MostafaELFEEL/Amusement-Park-Themed-Marble-Track/Images of CAD+CAD file/2.PNG

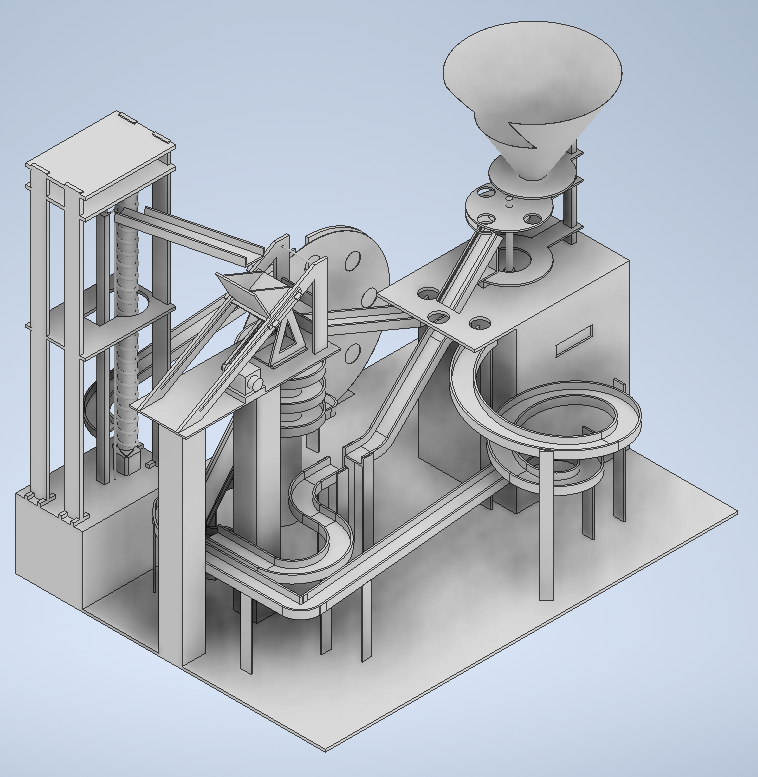
Images of CAD+CAD file/2.PNG
