MostafaELFEEL/Amusement-Park-Themed-Marble-Track/Images of CAD+CAD file/5.PNG

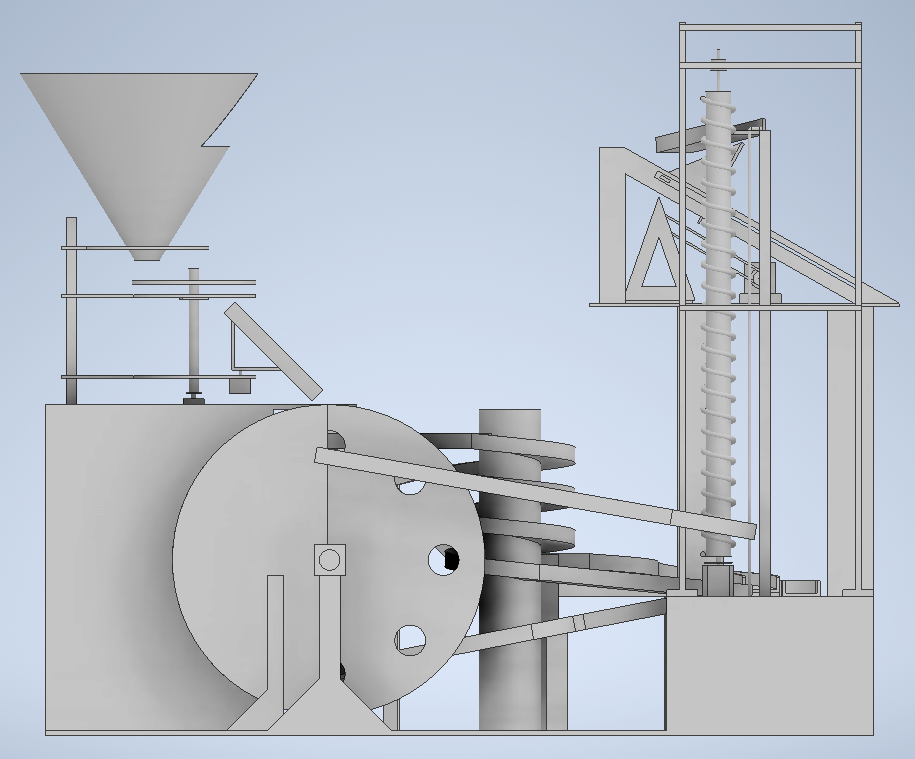
Images of CAD+CAD file/5.PNG
