MostafaELFEEL/Amusement-Park-Themed-Marble-Track/Images of CAD+CAD file/6.PNG

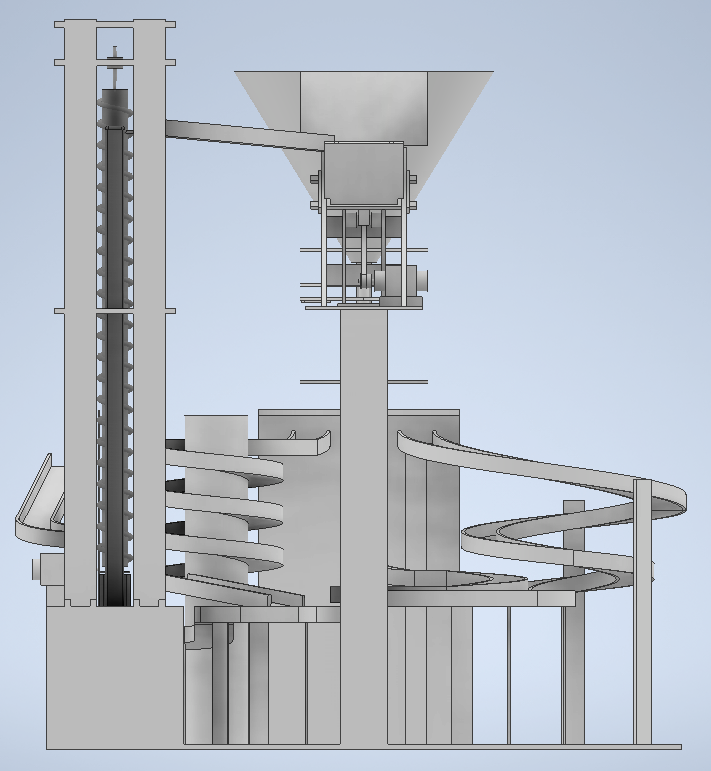
Images of CAD+CAD file/6.PNG
