MostafaELFEEL/Amusement-Park-Themed-Marble-Track/Images of CAD+CAD file/7.PNG

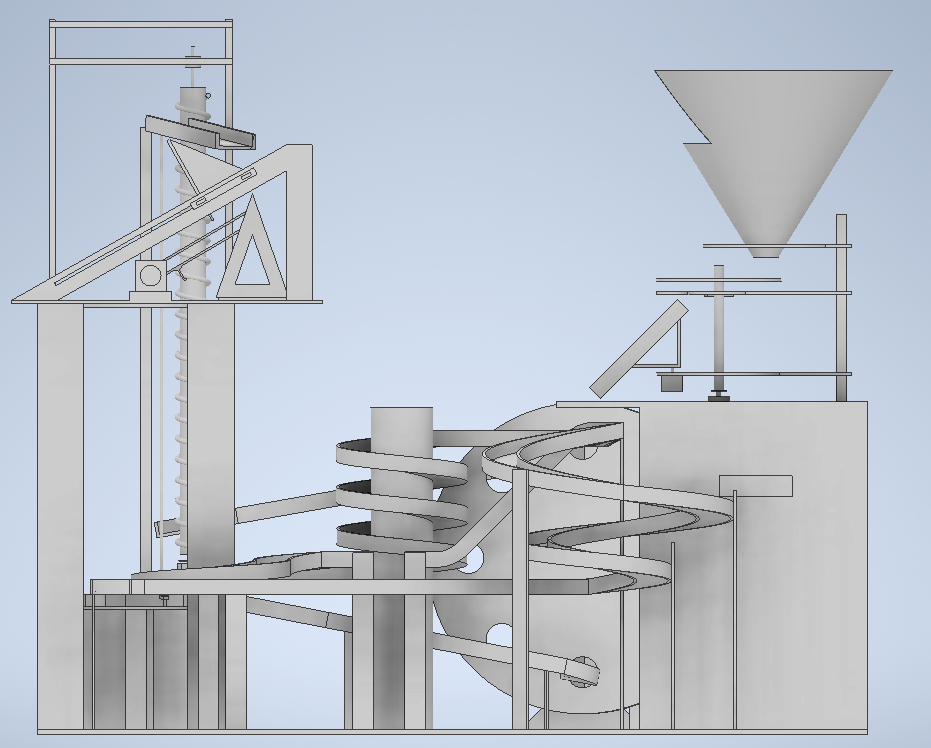
Images of CAD+CAD file/7.PNG
