MostafaELFEEL/Amusement-Park-Themed-Marble-Track/Images of CAD+CAD file/8.PNG

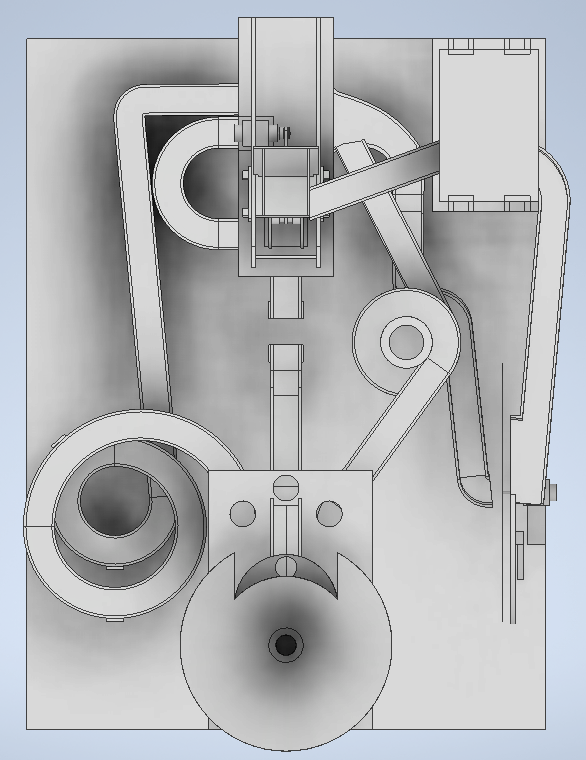
Images of CAD+CAD file/8.PNG
