MostafaELFEEL/Amusement-Park-Themed-Marble-Track/Images of CAD+CAD file/shooting 1.PNG

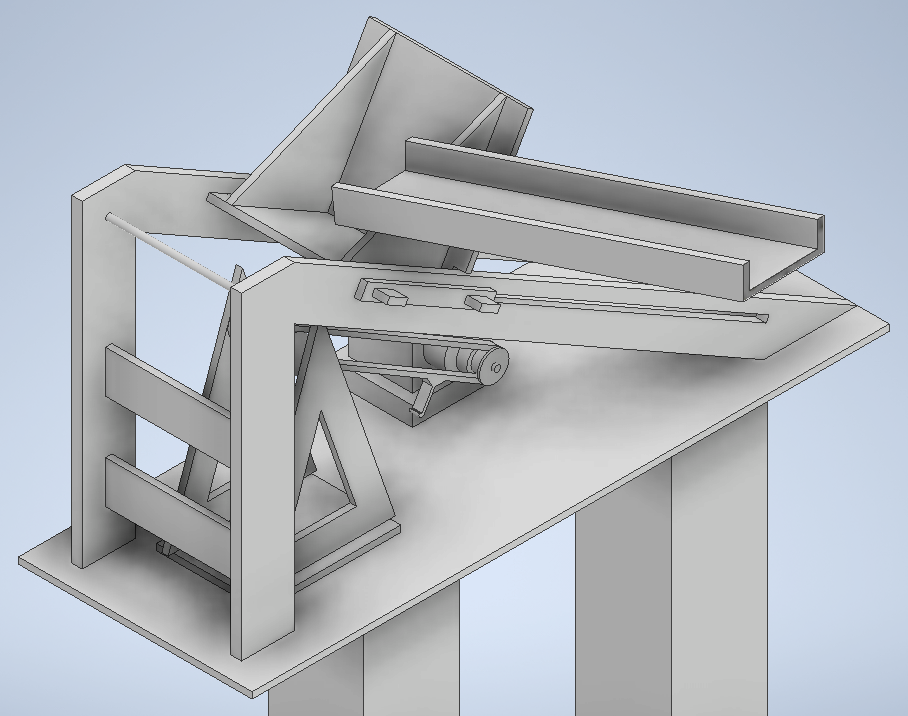
Images of CAD+CAD file/shooting 1.PNG
