MostafaELFEEL/Amusement-Park-Themed-Marble-Track/Images of CAD+CAD file/shooting 3.PNG

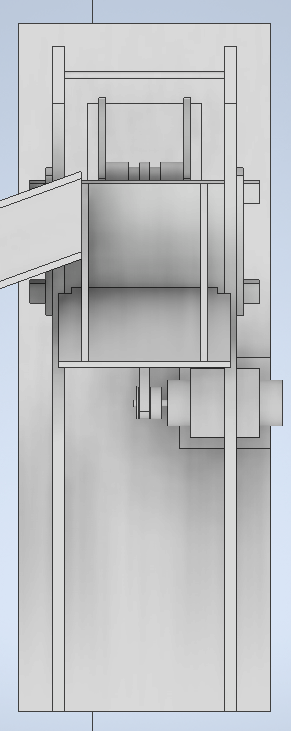
Images of CAD+CAD file/shooting 3.PNG
