MostafaELFEEL/Amusement-Park-Themed-Marble-Track/Images of CAD+CAD file/shooting 4.PNG

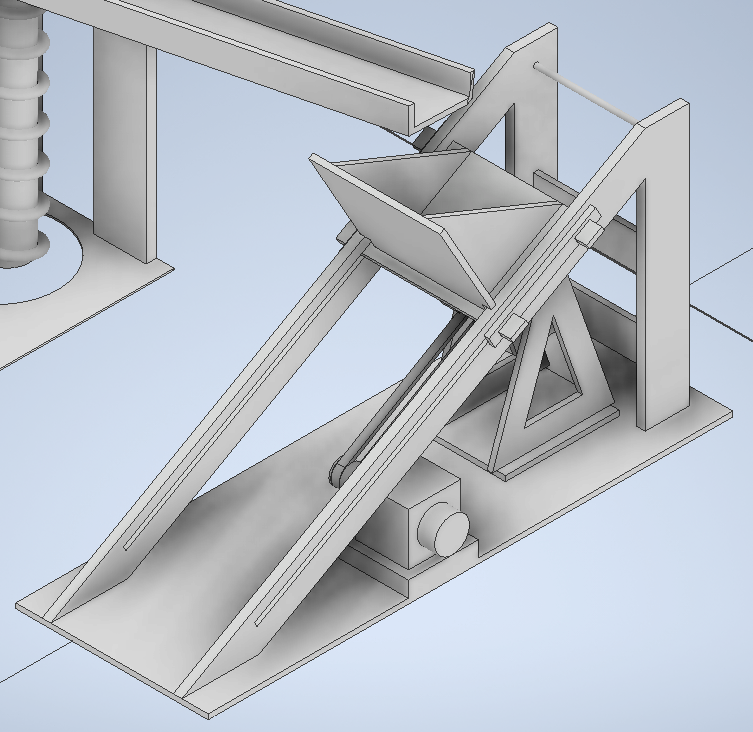
Images of CAD+CAD file/shooting 4.PNG
