MostafaELFEEL/Amusement-Park-Themed-Marble-Track/Images of CAD+CAD file/sorting system 0.PNG

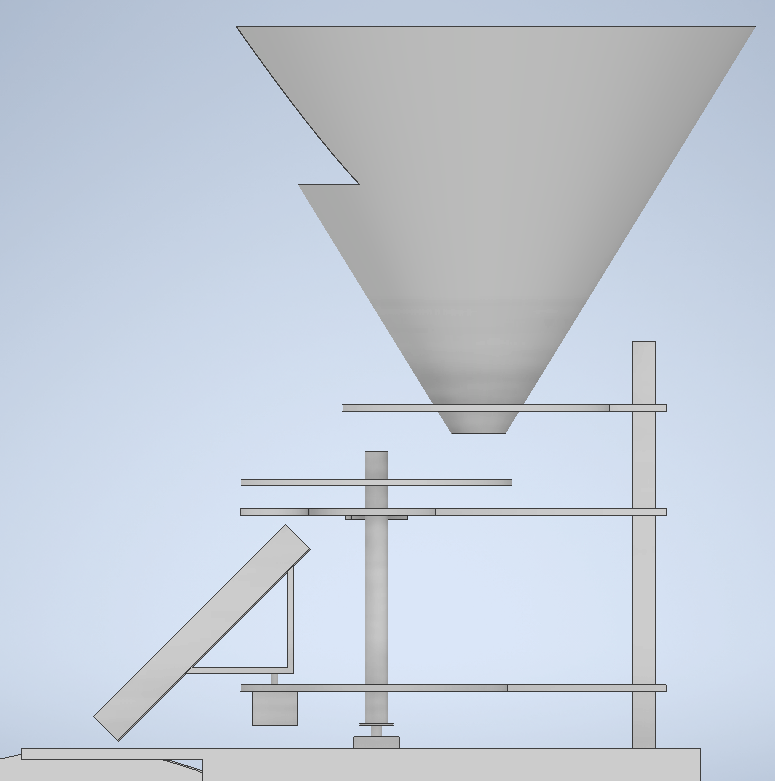
Images of CAD+CAD file/sorting system 0.PNG
