MostafaELFEEL/Amusement-Park-Themed-Marble-Track/Images of CAD+CAD file/sorting system 1.PNG

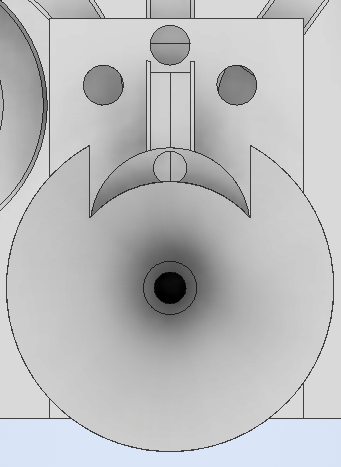
Images of CAD+CAD file/sorting system 1.PNG
