MostafaELFEEL/Amusement-Park-Themed-Marble-Track/Images of CAD+CAD file/wheel 1.PNG

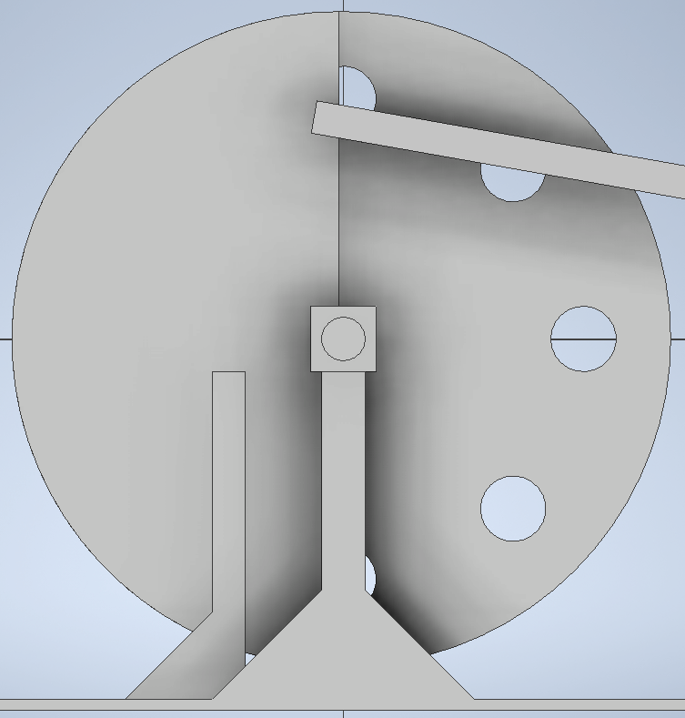
Images of CAD+CAD file/wheel 1.PNG
