MostafaELFEEL/Amusement-Park-Themed-Marble-Track/Images of CAD+CAD file/wheel 2.PNG

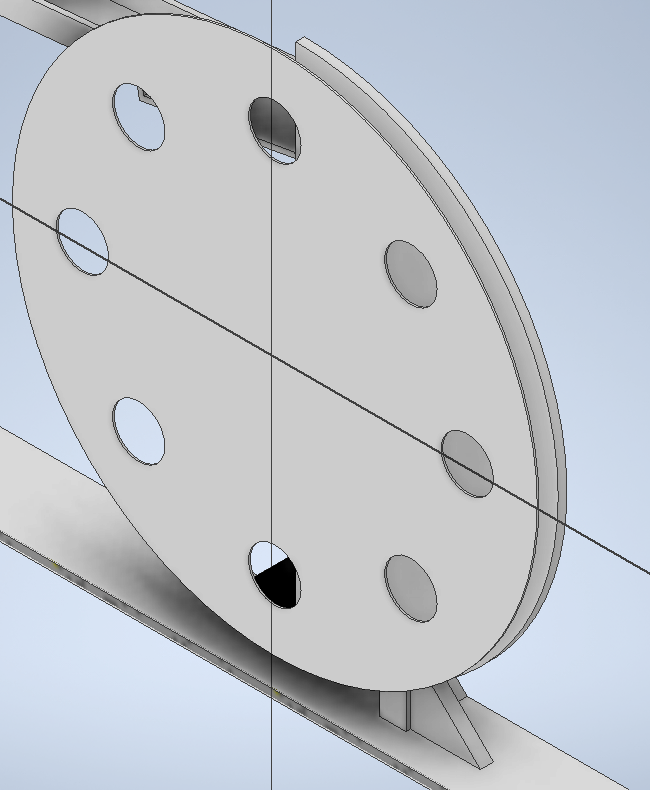
Images of CAD+CAD file/wheel 2.PNG
